TheColonelYoung/Kratos_pack/fw/kratos_pack/Src/config.hpp

/**
 * @file config.hpp
 * @author Petr Malaník (TheColonelYoung(at)gmail(dot)com)
 * @version 0.1
 * @date 12.07.2019
 *
 * @brief   This is default configuration for MCU, serves only as example how it should look
 *          MCU configuration is specific for every project and should be customized
 *          Project specific ,config should be located in Src folder with name config.hpp
 *          To this file is pointing symbolic link from this folder
 *
 */
#pragma once

// #define ADC_1_EN
// #define ADC_2_EN
// #define ADC_3_EN

// #define DAC_1_EN

// #define USB_CDC_EN

// #define UART_1_EN
#define UART_2_EN
#define UART_3_EN
// #define UART_4_EN

// #define TIM_1_EN
#define TIM_2_EN
// #define TIM_3_EN
// #define TIM_4_EN
// #define TIM_5_EN
// #define TIM_6_EN
// #define TIM_7_EN
// #define TIM_8_EN
// #define TIM_9_EN
// #define TIM_10_EN
// #define TIM_11_EN
// #define TIM_12_EN
// #define TIM_13_EN
// #define TIM_14_EN
// #define TIM_15_EN
// #define TIM_16_EN

#define I2C_1_EN
//#define I2C_2_EN
//#define I2C_3_EN
//#define I2C_4_EN

//#define SPI_1_EN
//#define SPI_2_EN
//#define SPI_3_EN
//#define SPI_4_EN


// # define FLASH_EN

// #define OTS_EN
